yoshun-jda/tomkey/img/build/188752_0.jpg

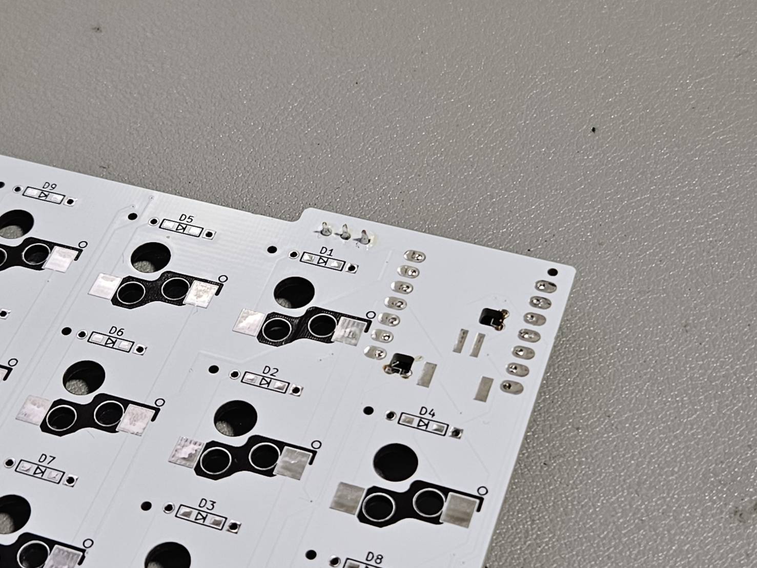
img/build/188752_0.jpg
