yoshun-jda/tomkey/img/build/188753_0.jpg

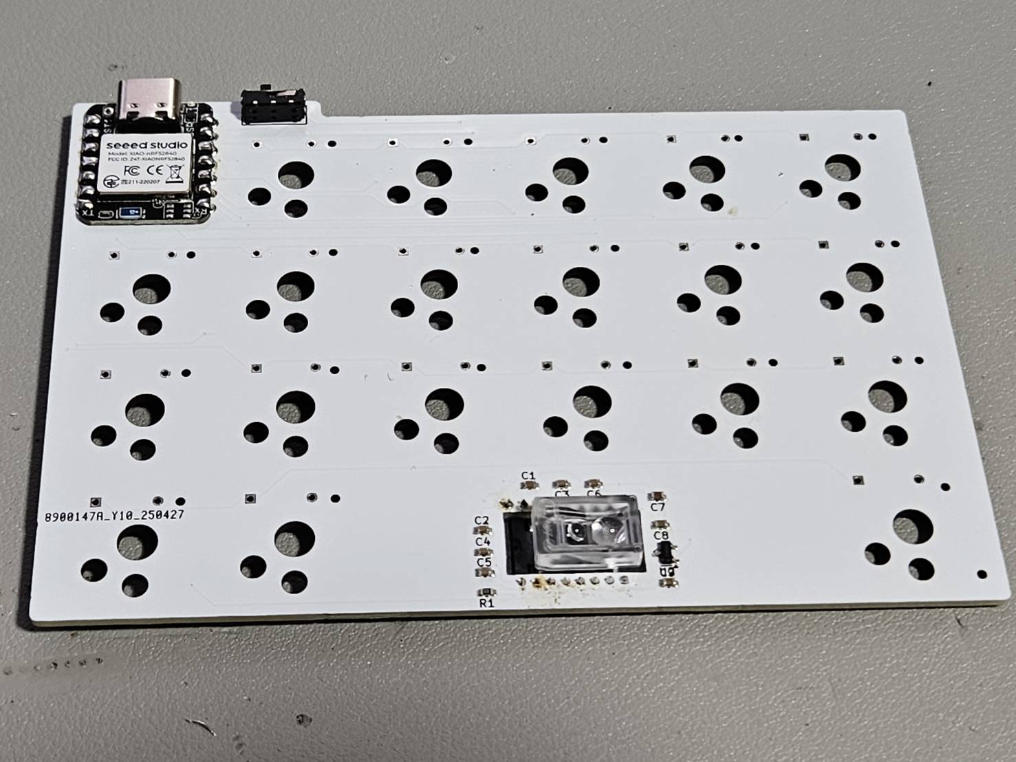
img/build/188753_0.jpg
