yoshun-jda/tomkey/img/build/188755_0.jpg

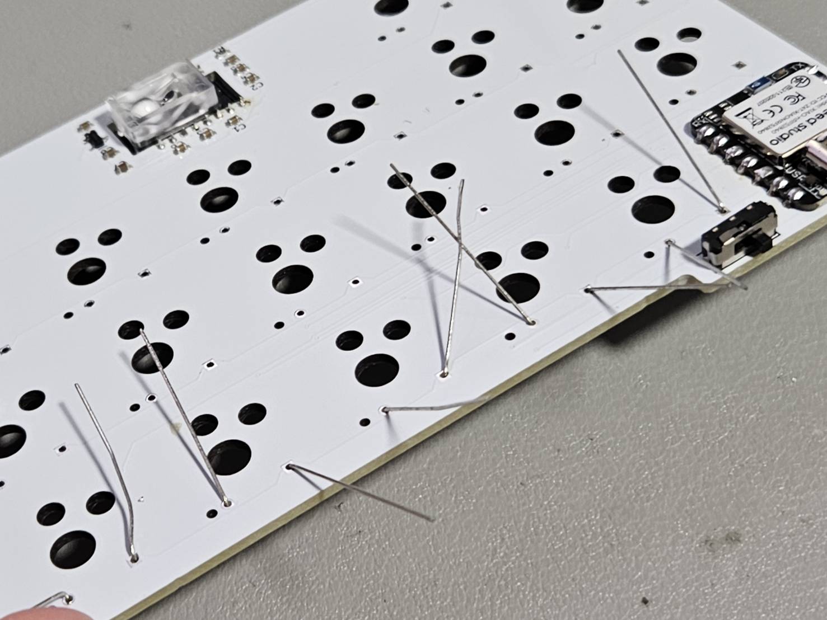
img/build/188755_0.jpg
