yoshun-jda/tomkey/img/build/188757_0.jpg

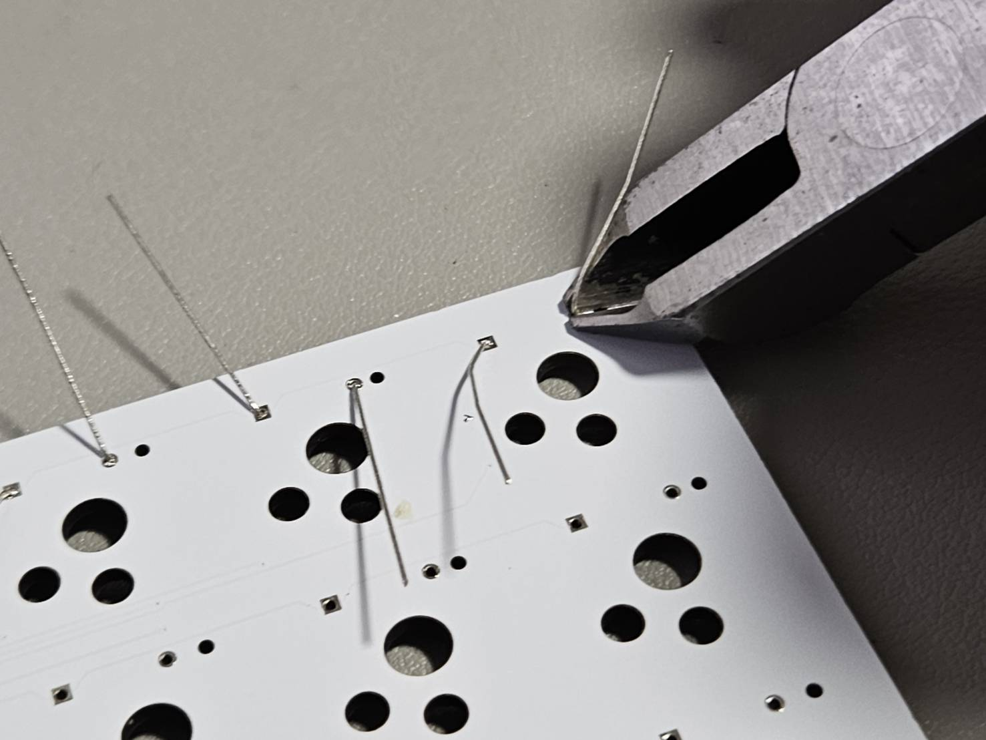
img/build/188757_0.jpg
