yoshun-jda/tomkey/img/build/188758_0.jpg

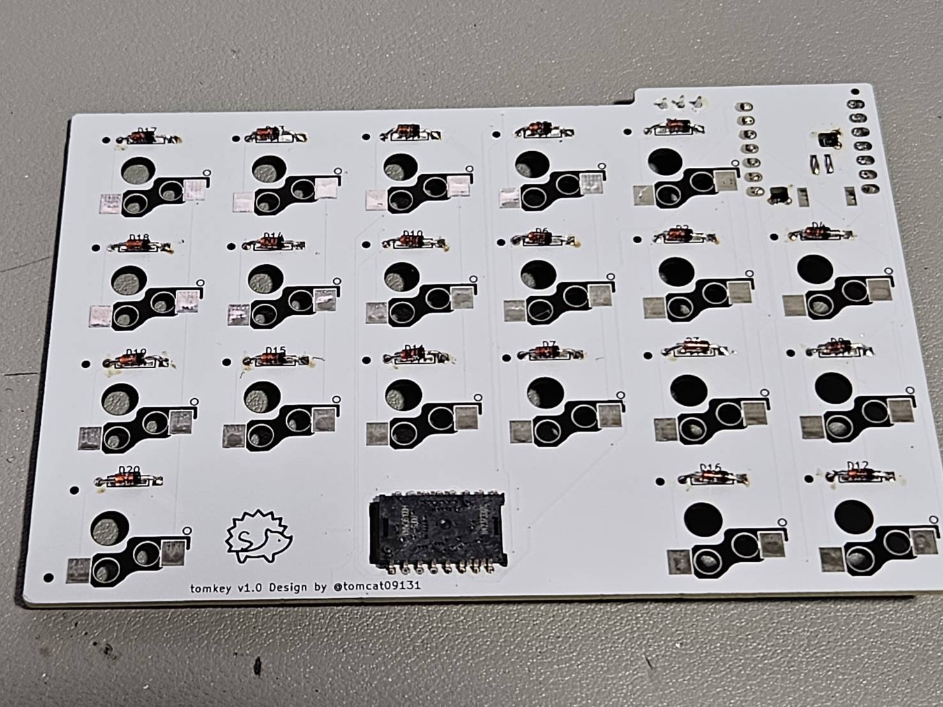
img/build/188758_0.jpg
