yoshun-jda/tomkey/img/build/188759_0.jpg

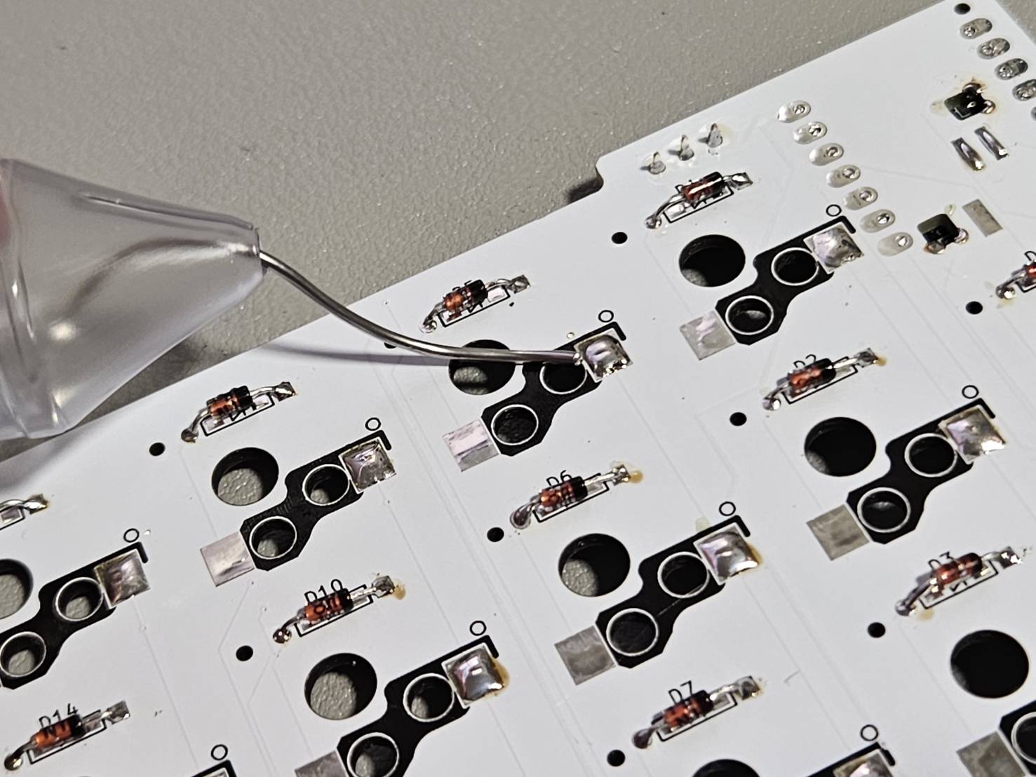
img/build/188759_0.jpg
