yoshun-jda/tomkey/img/build/188760_0.jpg

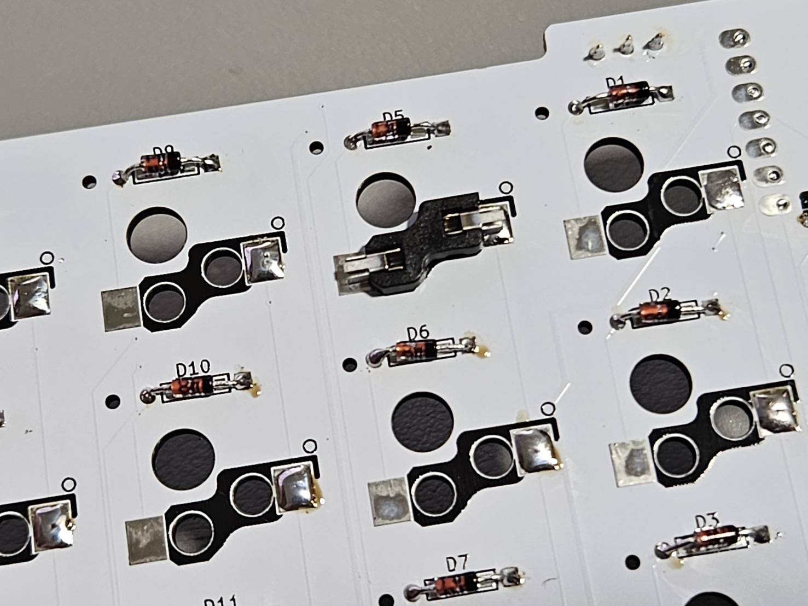
img/build/188760_0.jpg
