yoshun-jda/tomkey/img/build/188762_0.jpg

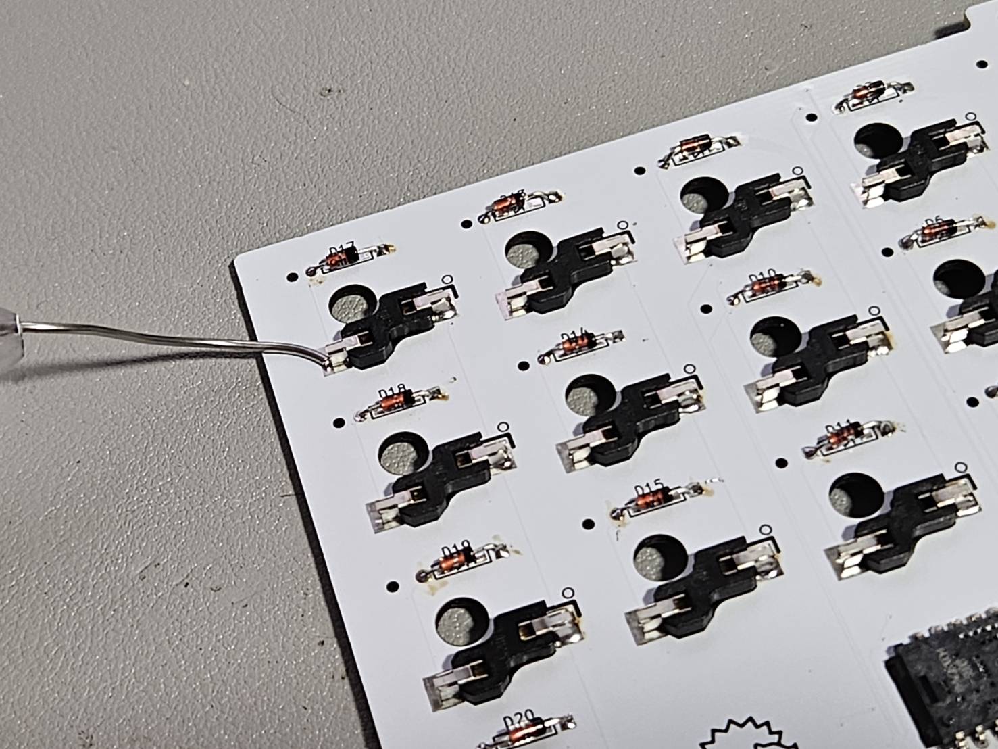
img/build/188762_0.jpg
