yoshun-jda/tomkey/img/build/188763_0.jpg

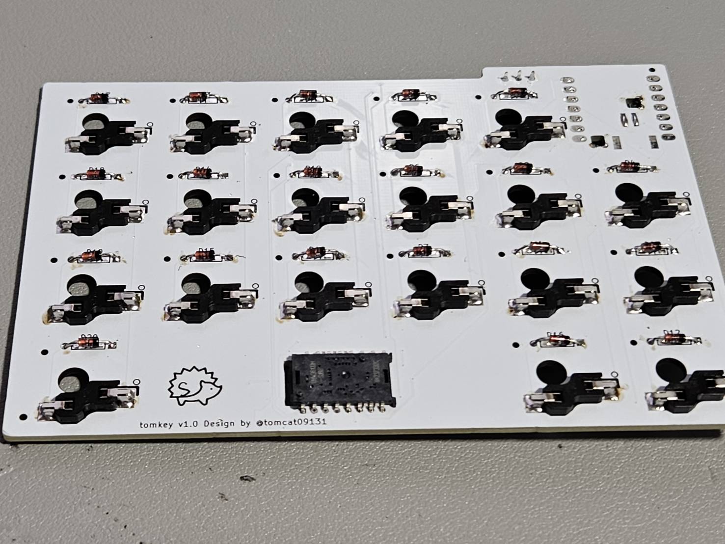
img/build/188763_0.jpg
