yoshun-jda/tomkey/img/build/188764_0.jpg

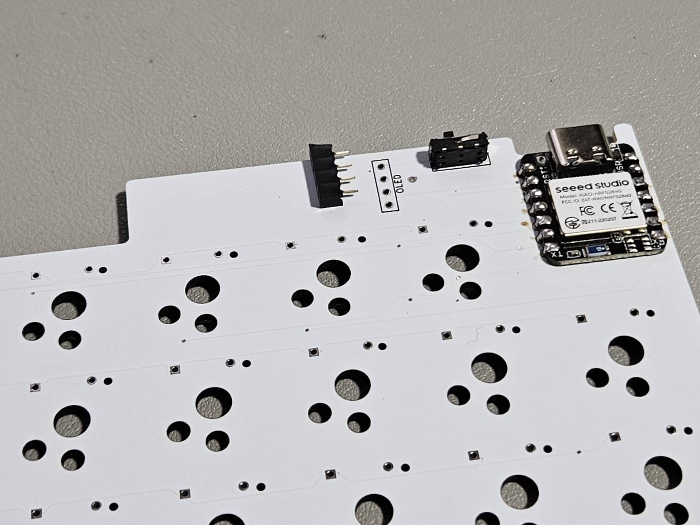
img/build/188764_0.jpg
