yoshun-jda/tomkey/img/build/188765_0.jpg

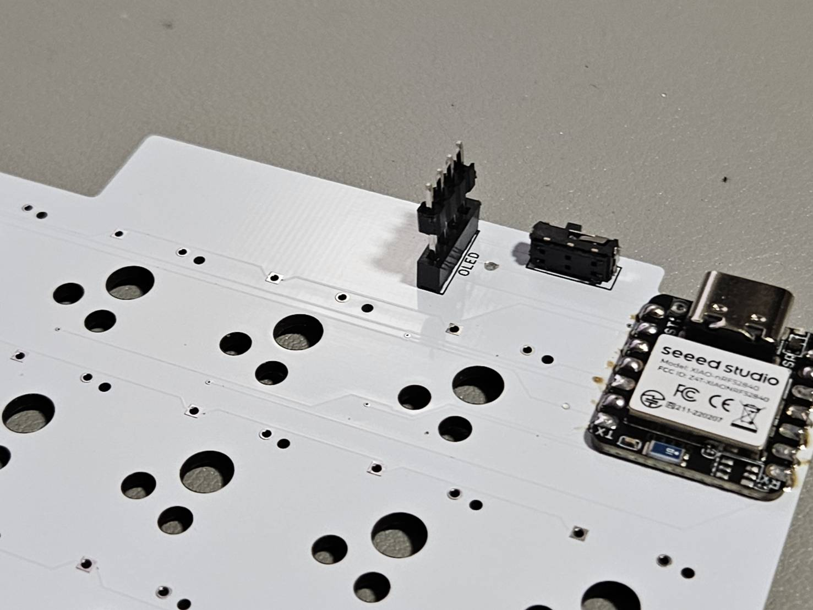
img/build/188765_0.jpg
