yoshun-jda/tomkey/img/build/188766_0.jpg

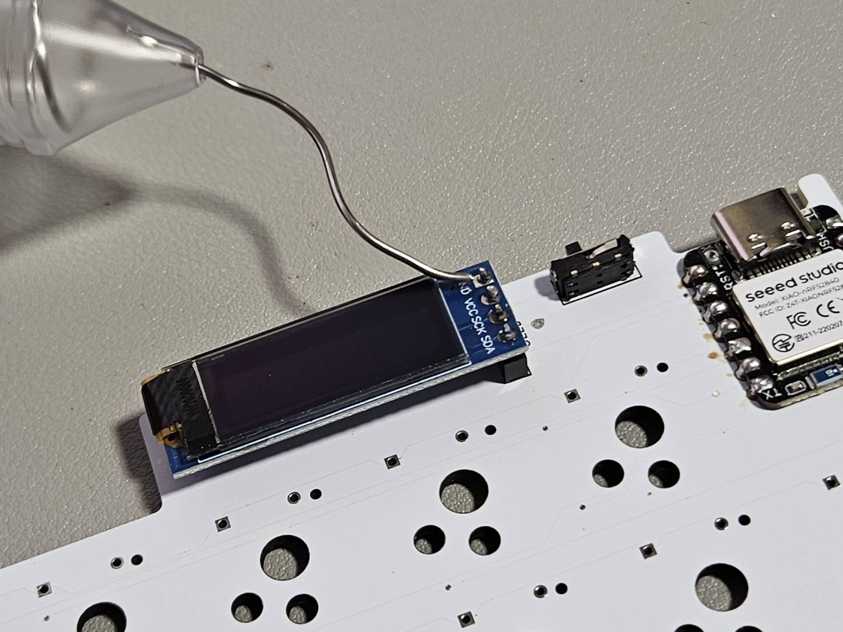
img/build/188766_0.jpg
