yoshun-jda/tomkey/img/build/188767_0.jpg

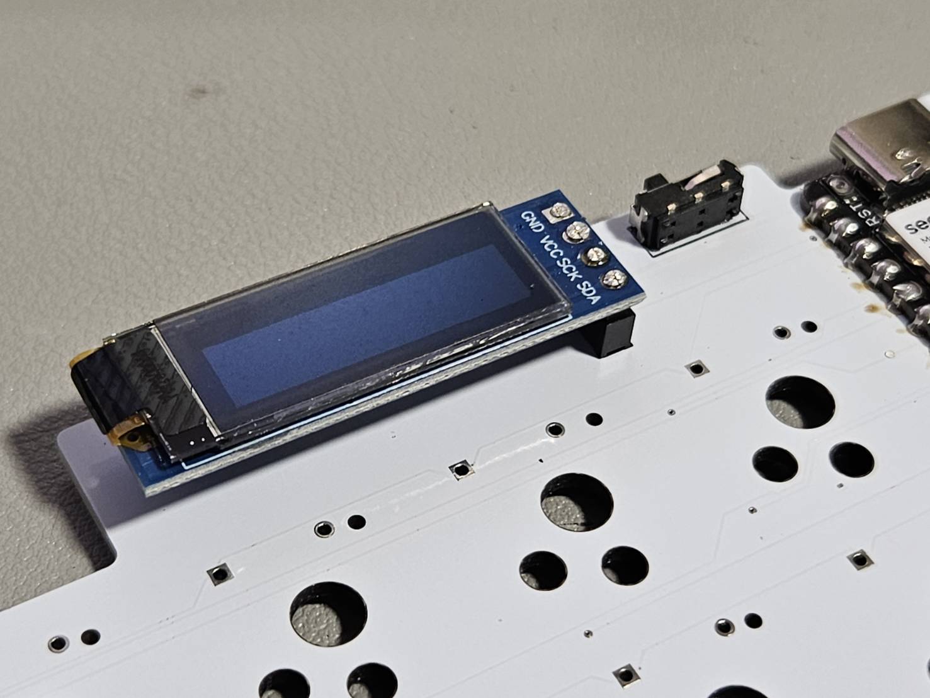
img/build/188767_0.jpg
