yoshun-jda/tomkey/img/build/188768_0.jpg

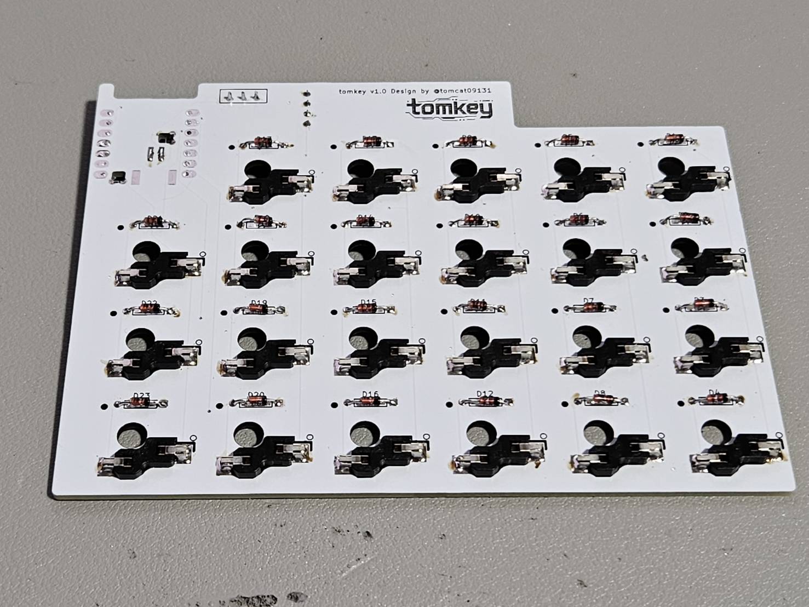
img/build/188768_0.jpg
