yoshun-jda/tomkey/img/build/188770_0.jpg

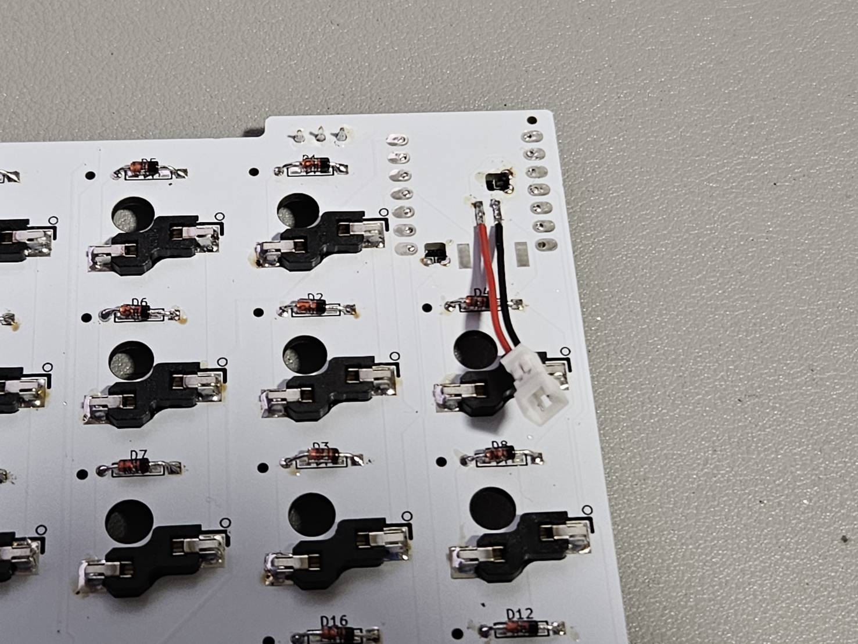
img/build/188770_0.jpg
