yoshun-jda/tomkey/img/build/188772_0.jpg

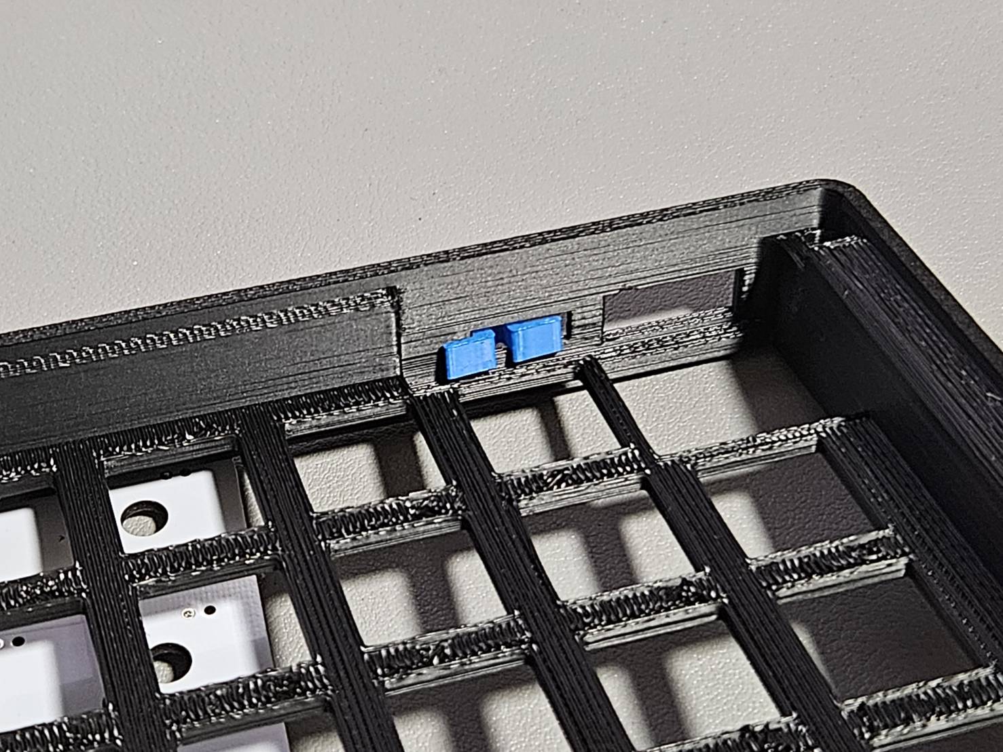
img/build/188772_0.jpg
