yoshun-jda/tomkey/img/build/188774_0.jpg

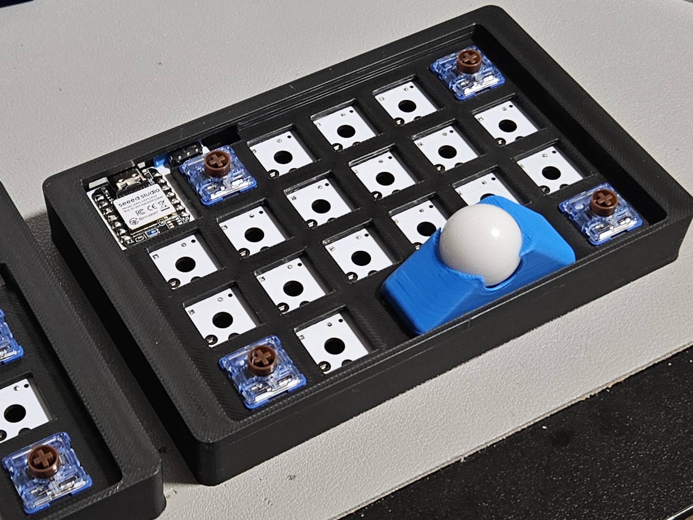
img/build/188774_0.jpg
