yoshun-jda/tomkey/img/build/exchangeTomkeyLk/189943_0.jpg

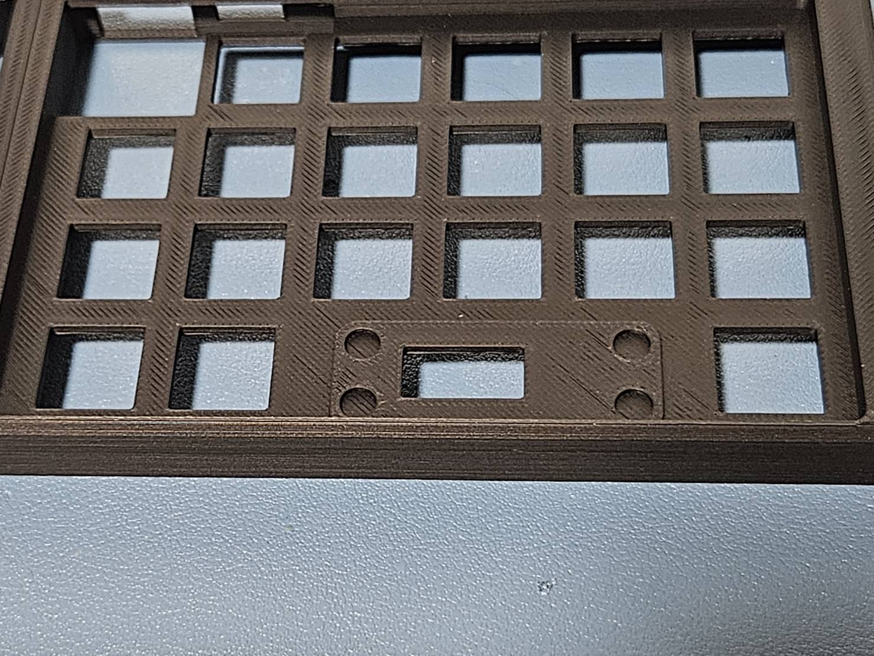
img/build/exchangeTomkeyLk/189943_0.jpg
